billjuv/EC_Fan_ESPHome/Attachments/IMG_1486.jpg

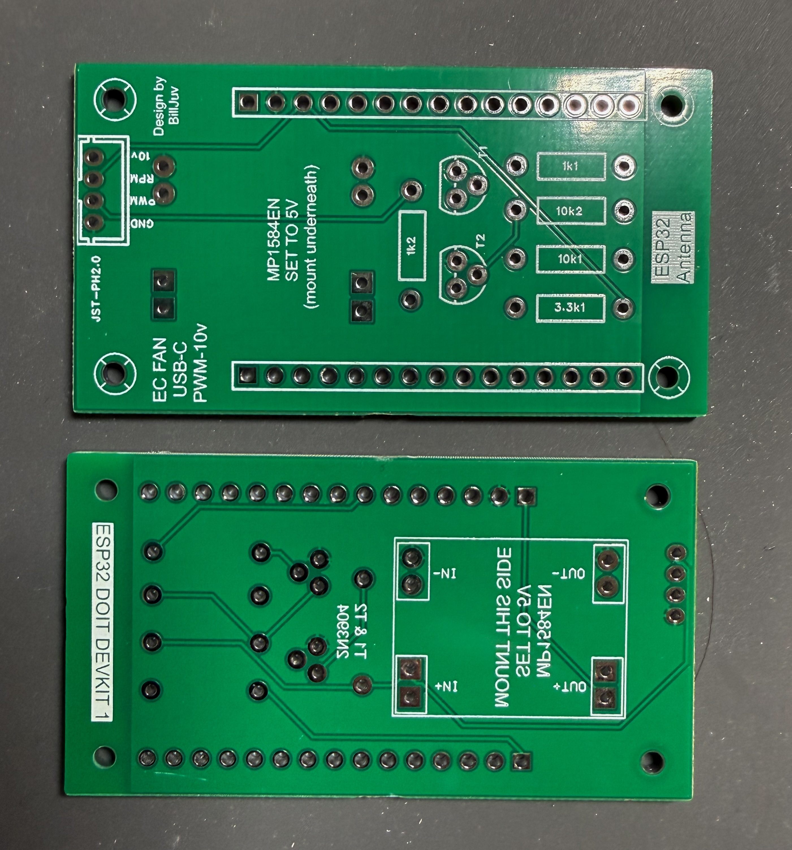
Attachments/IMG_1486.jpg
